hutuswatermelon/NT131.P22/back_end/uploads/1746864863473-entry-1746864863469.jpg

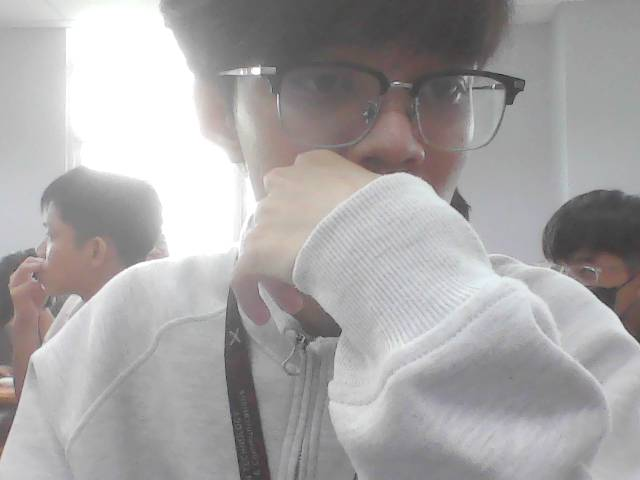
back_end/uploads/1746864863473-entry-1746864863469.jpg
