hutuswatermelon/NT131.P22/back_end/uploads/1746864864985-entry-1746864864979.jpg

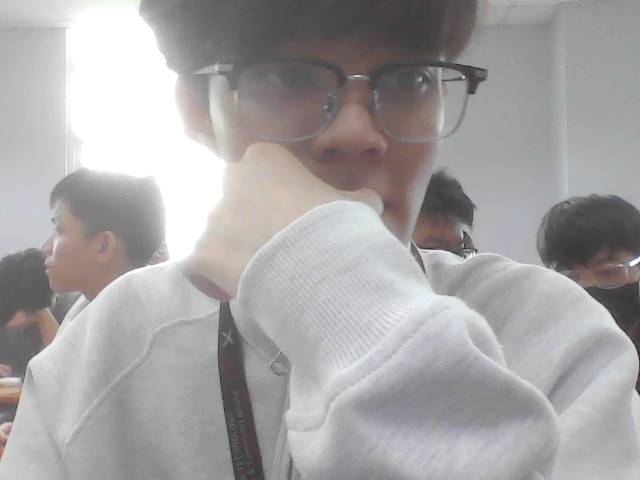
back_end/uploads/1746864864985-entry-1746864864979.jpg
