hutuswatermelon/NT131.P22/back_end/uploads/1746864866506-entry-1746864866501.jpg

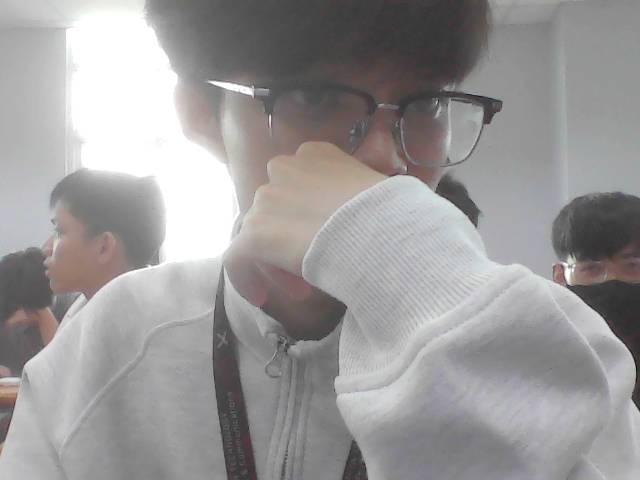
back_end/uploads/1746864866506-entry-1746864866501.jpg
