hutuswatermelon/NT131.P22/back_end/uploads/1746864868323-entry-1746864868013.jpg

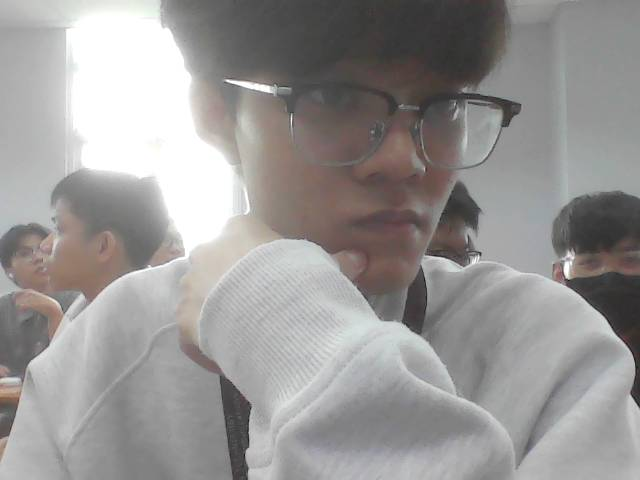
back_end/uploads/1746864868323-entry-1746864868013.jpg
