hutuswatermelon/NT131.P22/back_end/uploads/1746864869845-entry-1746864869527.jpg

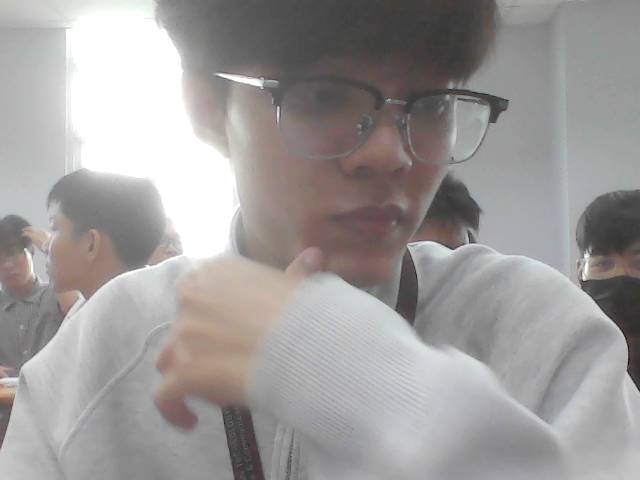
back_end/uploads/1746864869845-entry-1746864869527.jpg
