hutuswatermelon/NT131.P22/back_end/uploads/1746864871052-entry-1746864871045.jpg

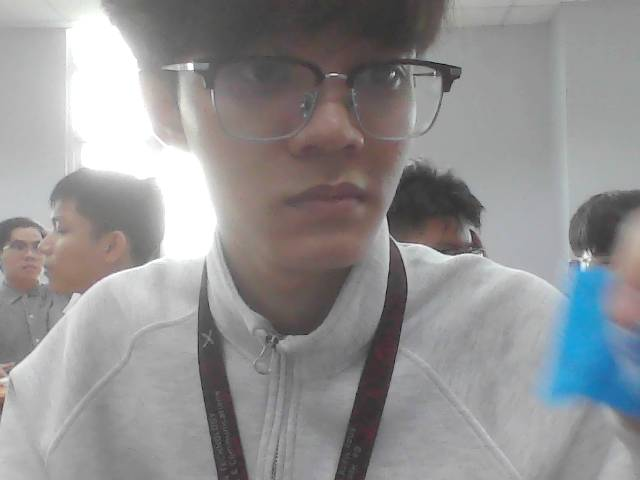
back_end/uploads/1746864871052-entry-1746864871045.jpg
