hutuswatermelon/NT131.P22/back_end/uploads/1746864872554-entry-1746864872549.jpg

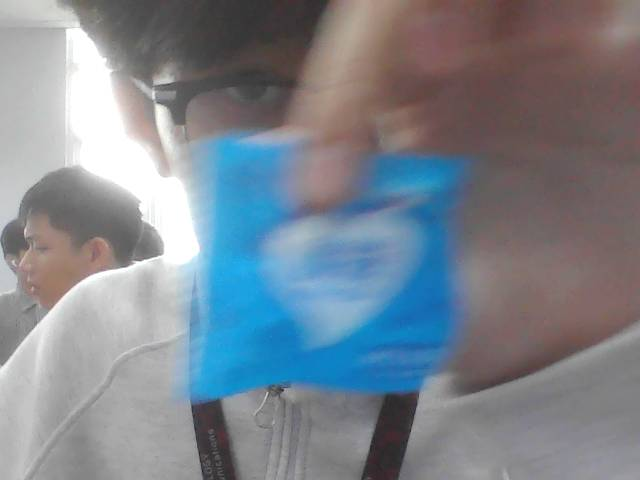
back_end/uploads/1746864872554-entry-1746864872549.jpg
