hutuswatermelon/NT131.P22/back_end/uploads/1746864874057-entry-1746864874053.jpg

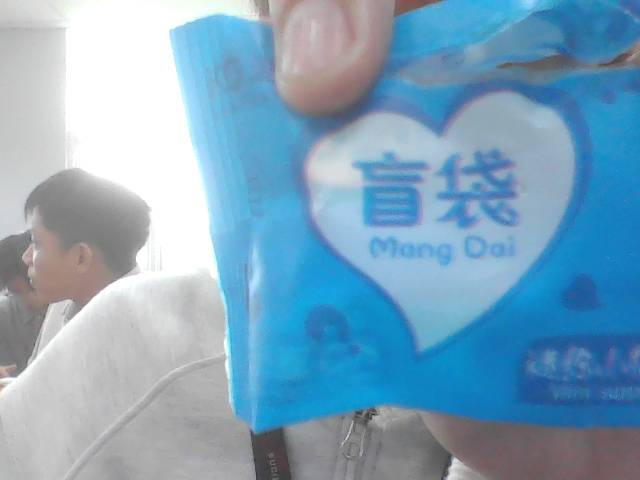
back_end/uploads/1746864874057-entry-1746864874053.jpg
