hutuswatermelon/NT131.P22/back_end/uploads/1746864875561-entry-1746864875557.jpg

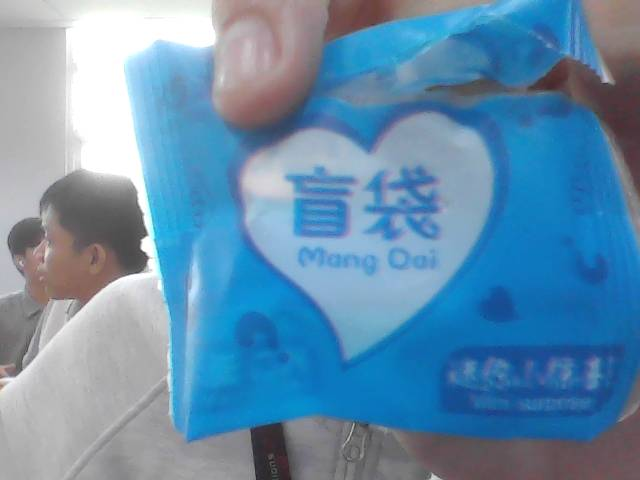
back_end/uploads/1746864875561-entry-1746864875557.jpg
