hutuswatermelon/NT131.P22/back_end/uploads/1746864877072-entry-1746864877068.jpg

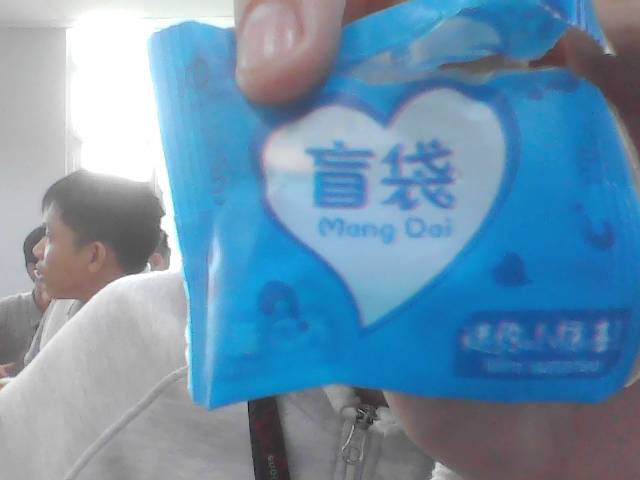
back_end/uploads/1746864877072-entry-1746864877068.jpg
