hutuswatermelon/NT131.P22/back_end/uploads/1746867527541-entry-1746867527536.jpg

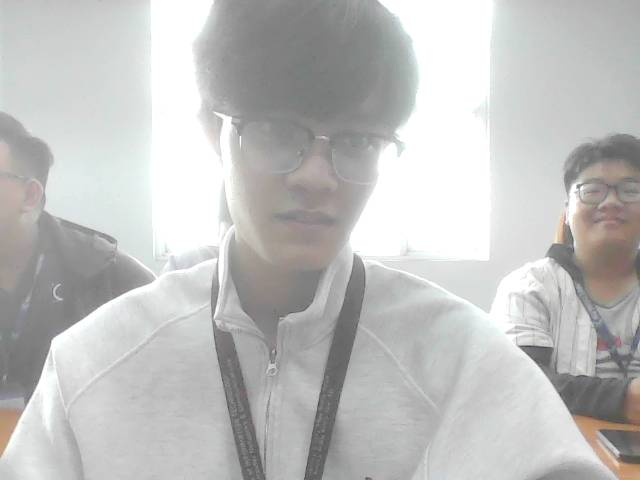
back_end/uploads/1746867527541-entry-1746867527536.jpg
