hutuswatermelon/NT131.P22/back_end/uploads/1746868455816-entry-1746868455803.jpg

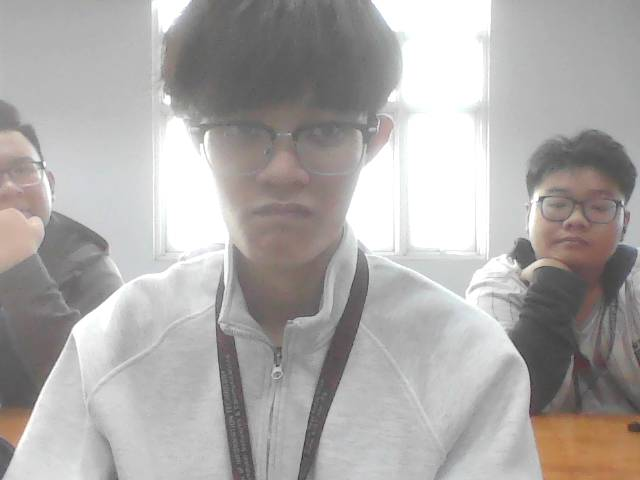
back_end/uploads/1746868455816-entry-1746868455803.jpg
