hutuswatermelon/NT131.P22/back_end/uploads/1746953575087-entry-1746953575075.jpg

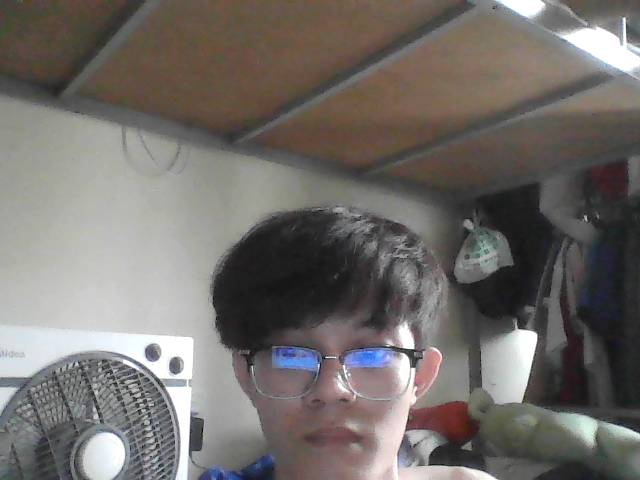
back_end/uploads/1746953575087-entry-1746953575075.jpg
