hutuswatermelon/NT131.P22/back_end/uploads/1746959261396-entry-1746959261392.jpg

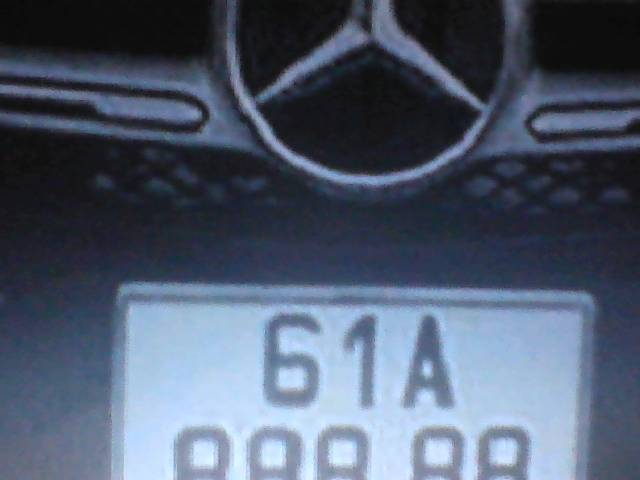
back_end/uploads/1746959261396-entry-1746959261392.jpg
