hutuswatermelon/NT131.P22/back_end/uploads/1746959275397-entry-1746959275392.jpg

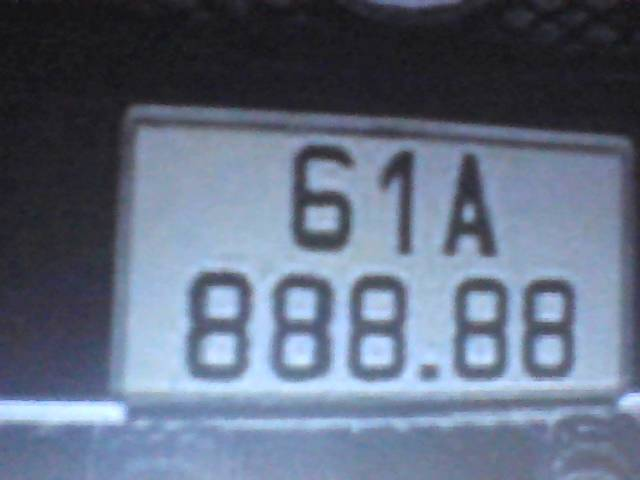
back_end/uploads/1746959275397-entry-1746959275392.jpg
