hutuswatermelon/NT131.P22/back_end/uploads/1746959362127-entry-1746959362123.jpg

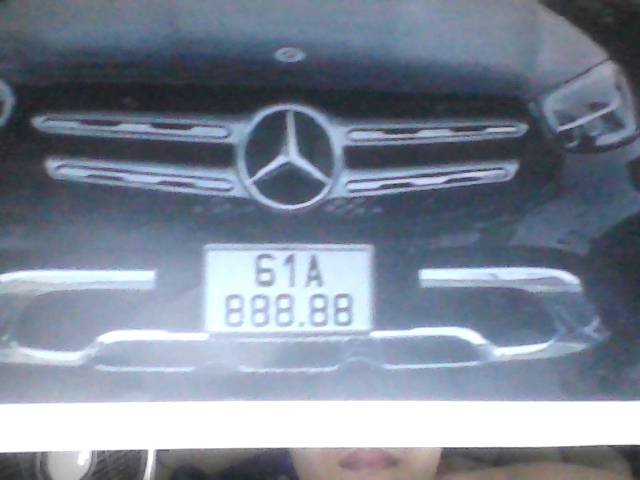
back_end/uploads/1746959362127-entry-1746959362123.jpg
