hutuswatermelon/NT131.P22/back_end/uploads/1746978081845-entry-1746978081831.jpg

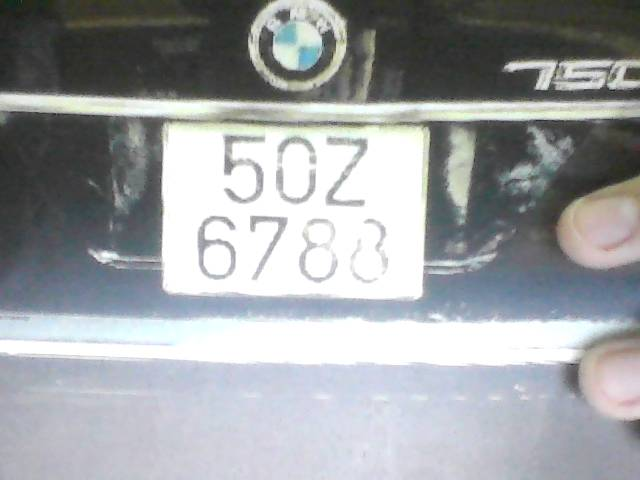
back_end/uploads/1746978081845-entry-1746978081831.jpg
