hutuswatermelon/NT131.P22/back_end/uploads/1746978145780-entry-1746978145776.jpg

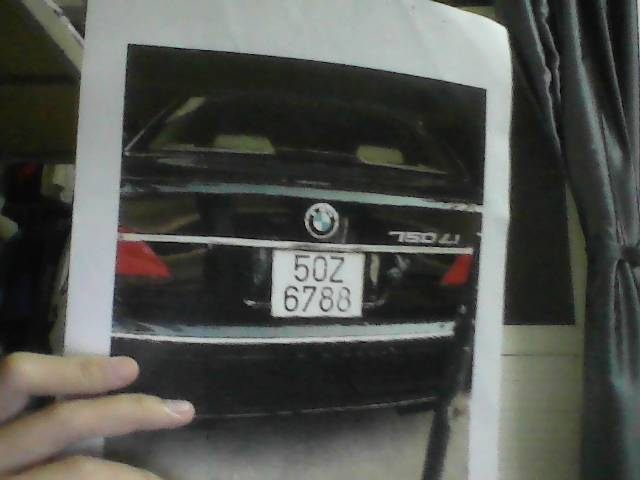
back_end/uploads/1746978145780-entry-1746978145776.jpg
