hutuswatermelon/NT131.P22/back_end/uploads/1746978197605-entry-1746978197599.jpg

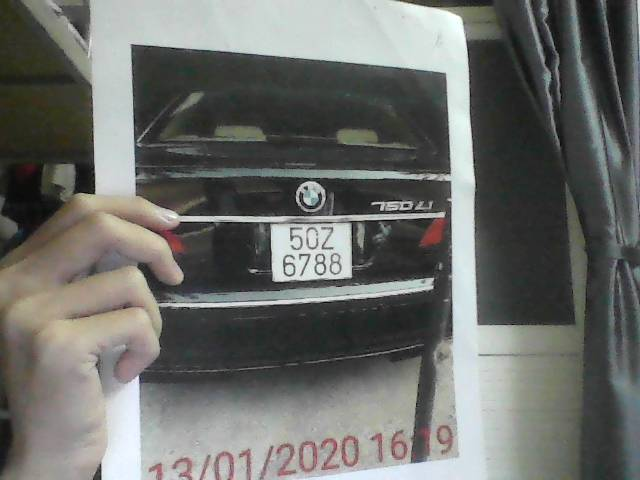
back_end/uploads/1746978197605-entry-1746978197599.jpg
