hutuswatermelon/NT131.P22/back_end/uploads/1746978227795-entry-1746978227792.jpg

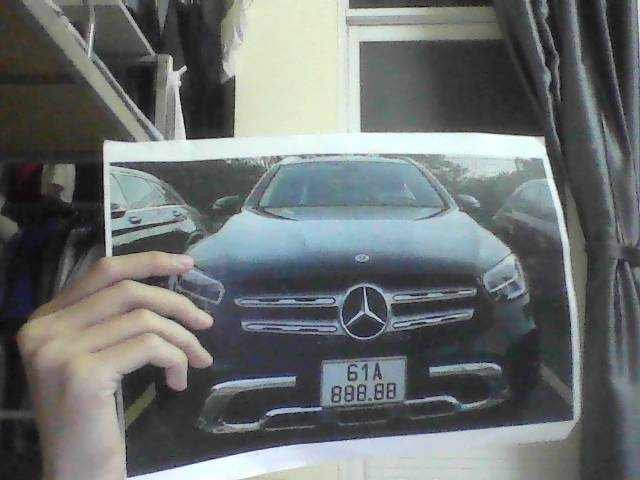
back_end/uploads/1746978227795-entry-1746978227792.jpg
