hutuswatermelon/NT131.P22/back_end/uploads/1746978264536-entry-1746978264530.jpg

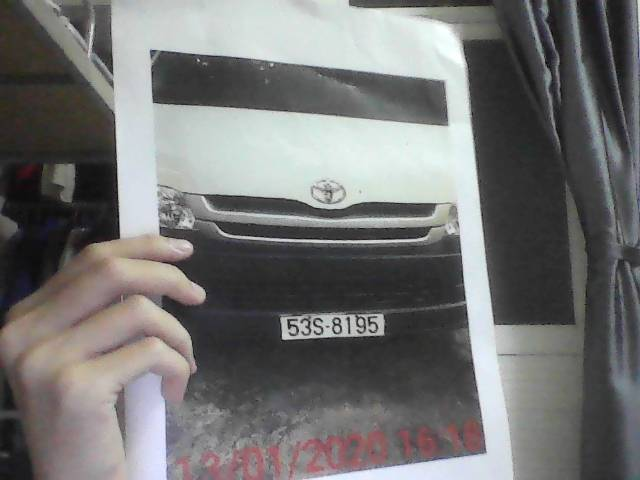
back_end/uploads/1746978264536-entry-1746978264530.jpg
