hutuswatermelon/NT131.P22/back_end/uploads/1746978326046-entry-1746978326043.jpg

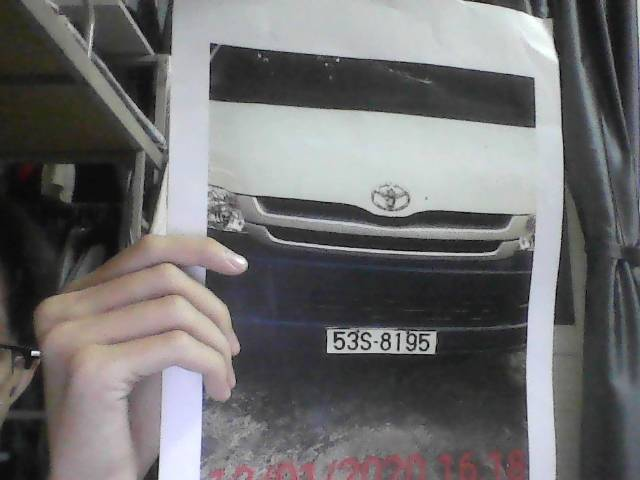
back_end/uploads/1746978326046-entry-1746978326043.jpg
