hutuswatermelon/NT131.P22/back_end/uploads/1746978920150-entry-1746978920143.jpg

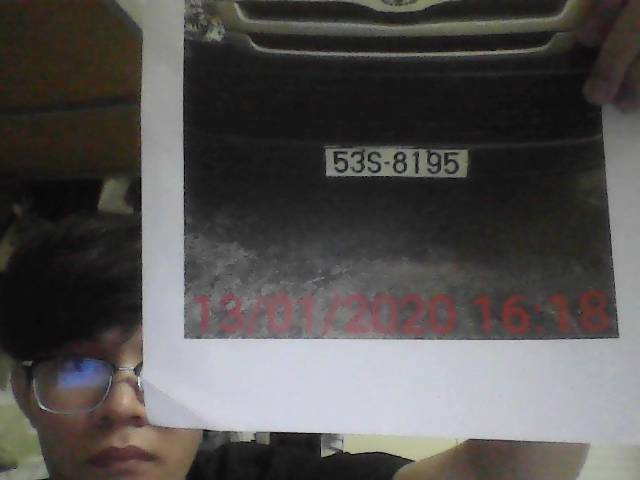
back_end/uploads/1746978920150-entry-1746978920143.jpg
