hutuswatermelon/NT131.P22/back_end/uploads/1746978947929-entry-1746978947927.jpg

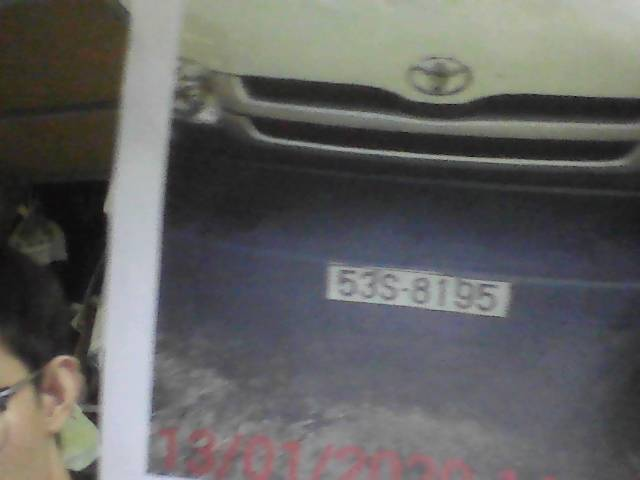
back_end/uploads/1746978947929-entry-1746978947927.jpg
