hutuswatermelon/NT131.P22/back_end/uploads/1746978972538-entry-1746978972531.jpg

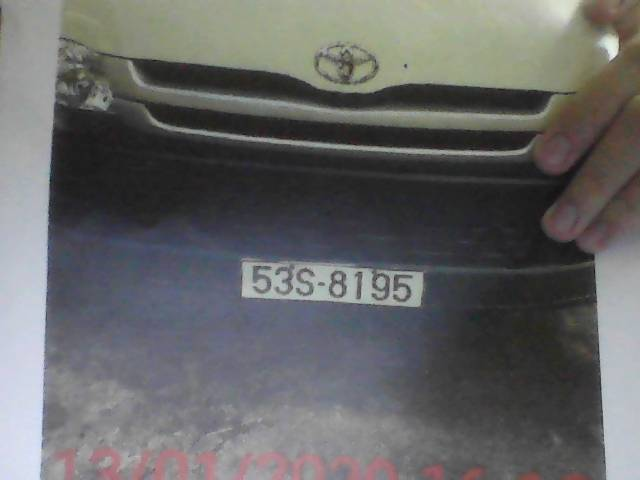
back_end/uploads/1746978972538-entry-1746978972531.jpg
