hutuswatermelon/NT131.P22/back_end/uploads/1746979031061-entry-1746979031053.jpg

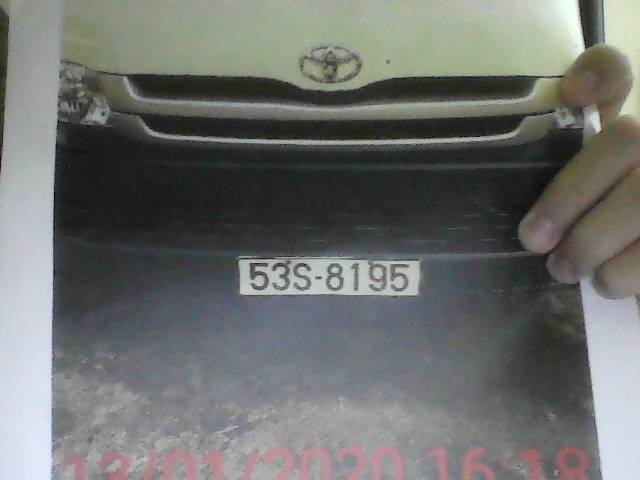
back_end/uploads/1746979031061-entry-1746979031053.jpg
