hutuswatermelon/NT131.P22/back_end/uploads/1746981746926-entry-1746981746917.jpg

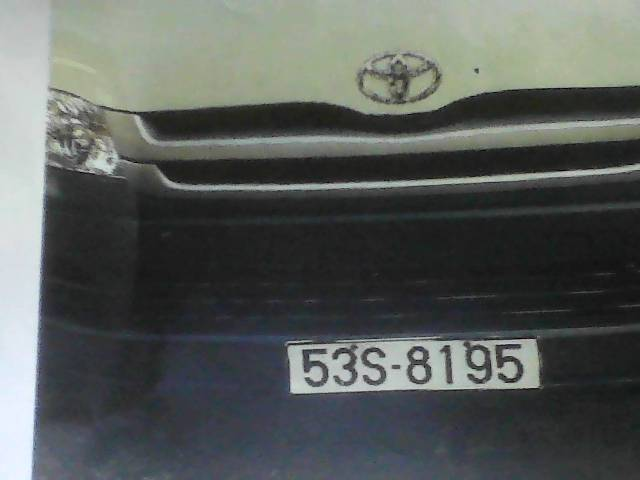
back_end/uploads/1746981746926-entry-1746981746917.jpg
