hutuswatermelon/NT131.P22/back_end/uploads/1746981779292-entry-1746981779285.jpg

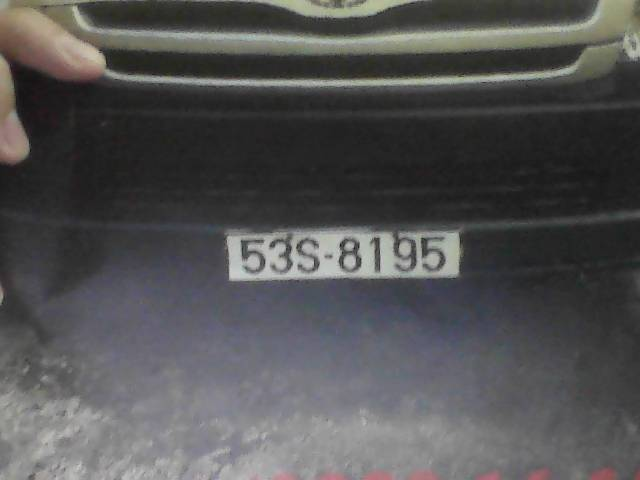
back_end/uploads/1746981779292-entry-1746981779285.jpg
