hutuswatermelon/NT131.P22/back_end/uploads/1746981790187-entry-1746981790183.jpg

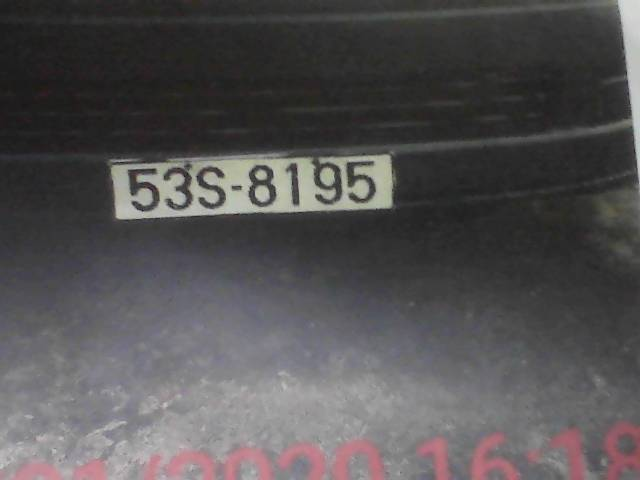
back_end/uploads/1746981790187-entry-1746981790183.jpg
