hutuswatermelon/NT131.P22/back_end/uploads/1746981802821-entry-1746981802512.jpg

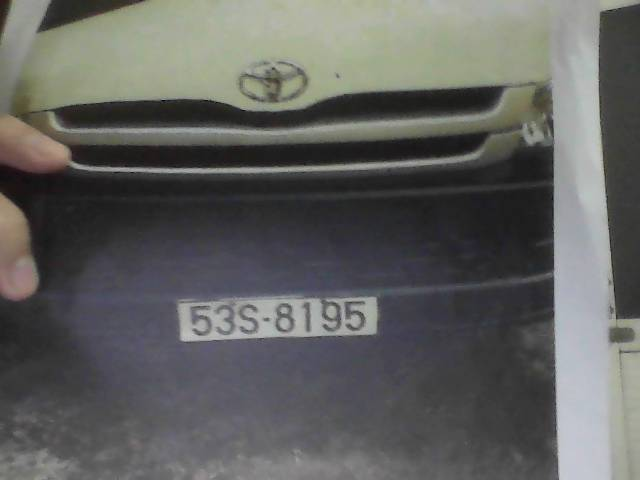
back_end/uploads/1746981802821-entry-1746981802512.jpg
