hutuswatermelon/NT131.P22/back_end/uploads/1746981819778-entry-1746981819770.jpg

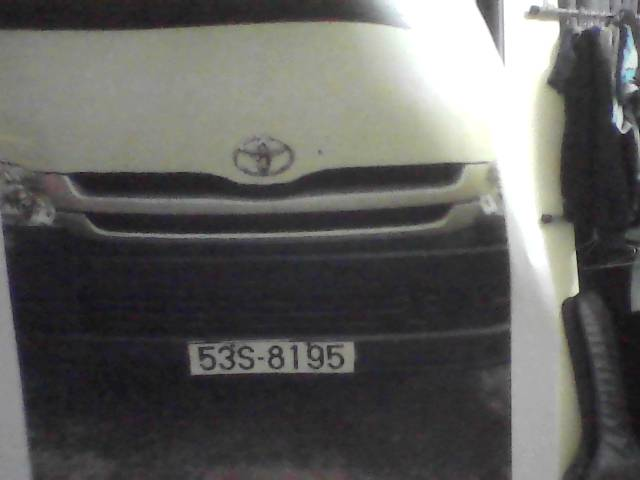
back_end/uploads/1746981819778-entry-1746981819770.jpg
