hutuswatermelon/NT131.P22/back_end/uploads/1746982269582-entry-1746982269579.jpg

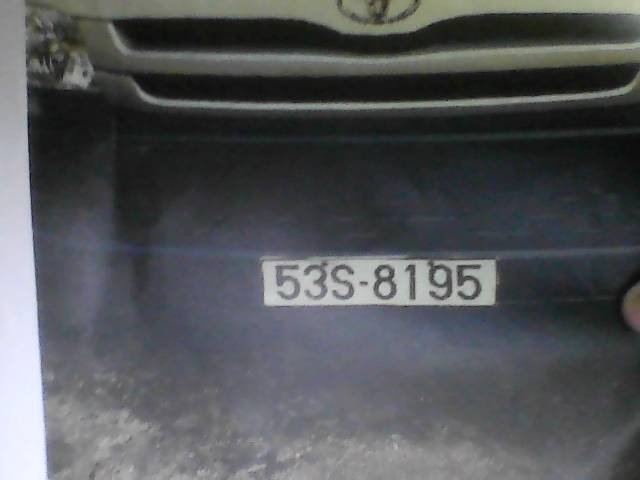
back_end/uploads/1746982269582-entry-1746982269579.jpg
