hutuswatermelon/NT131.P22/back_end/uploads/1746982297239-entry-1746982297234.jpg

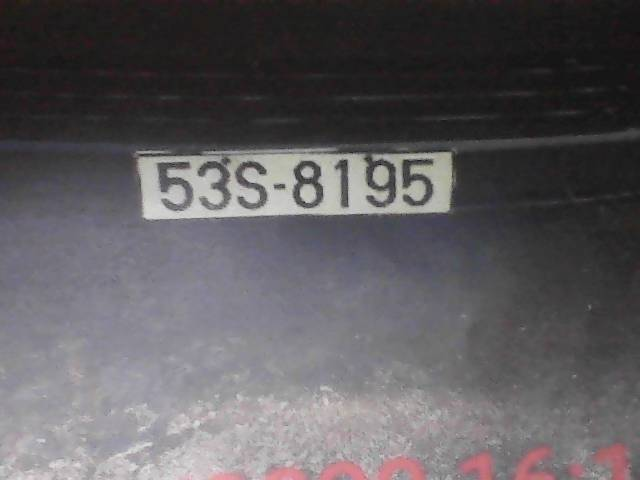
back_end/uploads/1746982297239-entry-1746982297234.jpg
