hutuswatermelon/NT131.P22/back_end/uploads/1746982308922-entry-1746982308920.jpg

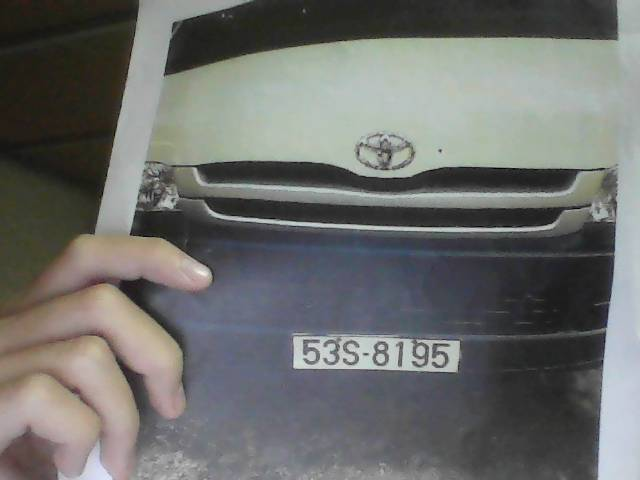
back_end/uploads/1746982308922-entry-1746982308920.jpg
