hutuswatermelon/NT131.P22/back_end/uploads/1746982318628-entry-1746982318623.jpg

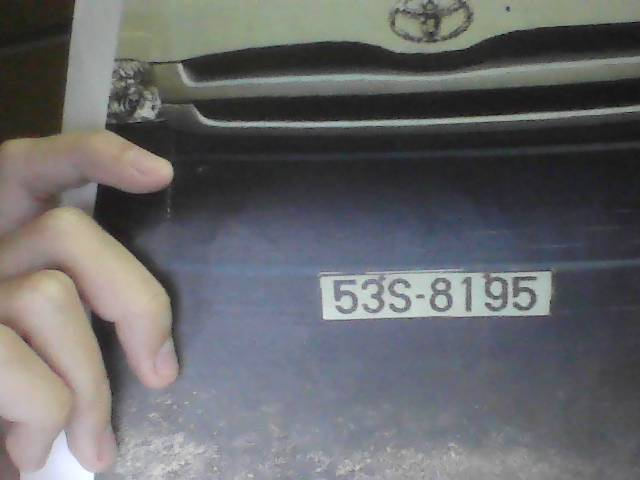
back_end/uploads/1746982318628-entry-1746982318623.jpg
