hutuswatermelon/NT131.P22/back_end/uploads/1746982329878-entry-1746982329874.jpg

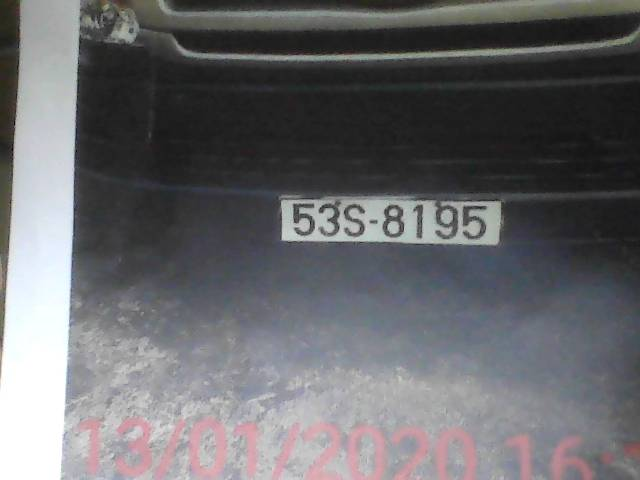
back_end/uploads/1746982329878-entry-1746982329874.jpg
