hutuswatermelon/NT131.P22/back_end/uploads/1746982339927-entry-1746982339925.jpg

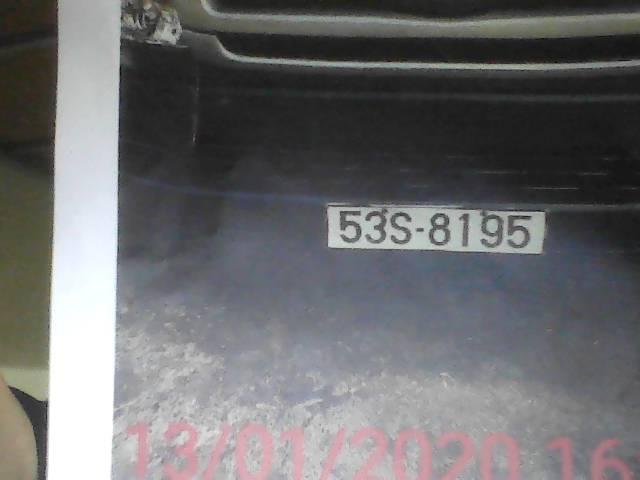
back_end/uploads/1746982339927-entry-1746982339925.jpg
