hutuswatermelon/NT131.P22/back_end/uploads/1746982353290-entry-1746982353286.jpg

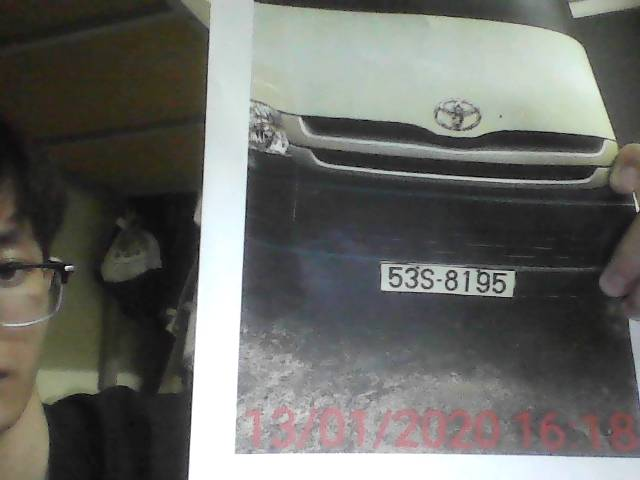
back_end/uploads/1746982353290-entry-1746982353286.jpg
