hutuswatermelon/NT131.P22/back_end/uploads/1746990870169-entry-1746990870156.jpg

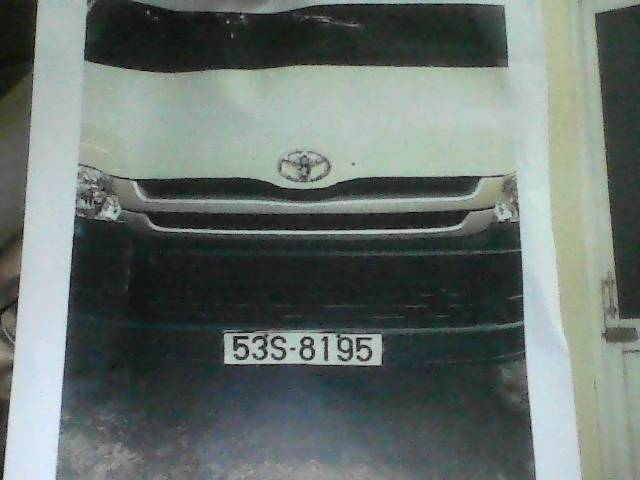
back_end/uploads/1746990870169-entry-1746990870156.jpg
