hutuswatermelon/NT131.P22/back_end/uploads/1746990877798-entry-1746990877794.jpg

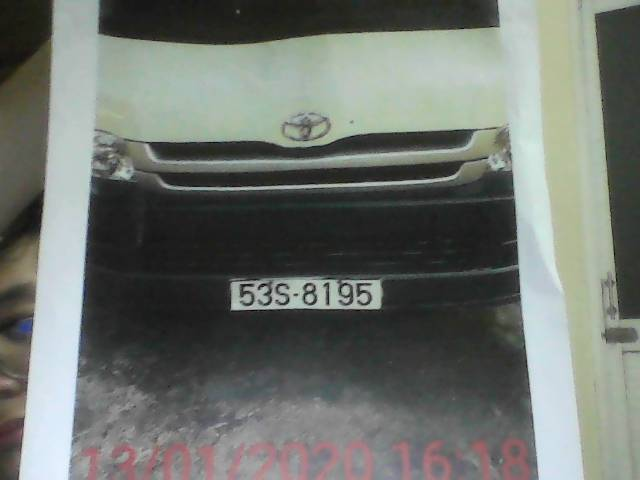
back_end/uploads/1746990877798-entry-1746990877794.jpg
