hutuswatermelon/NT131.P22/back_end/uploads/1746990892995-entry-1746990892991.jpg

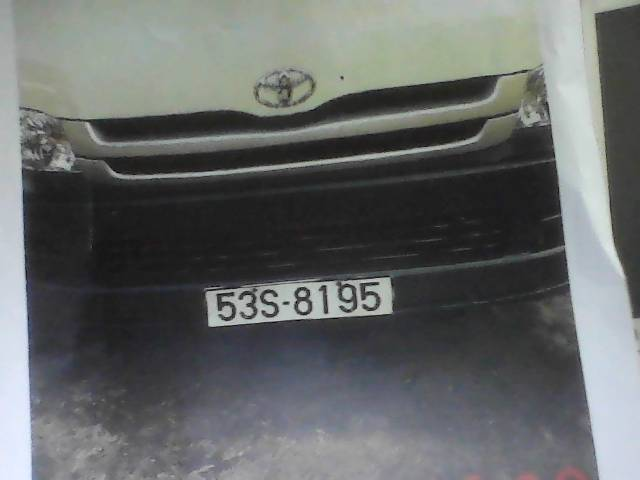
back_end/uploads/1746990892995-entry-1746990892991.jpg
