hutuswatermelon/NT131.P22/back_end/uploads/1746990904815-entry-1746990904812.jpg

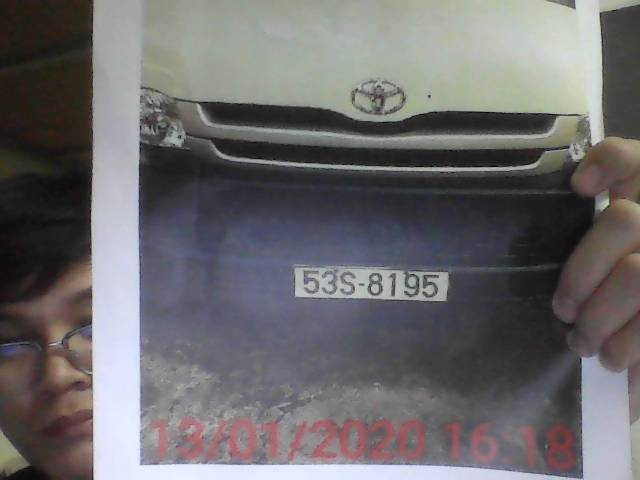
back_end/uploads/1746990904815-entry-1746990904812.jpg
