hutuswatermelon/NT131.P22/back_end/uploads/1746990915697-entry-1746990915695.jpg

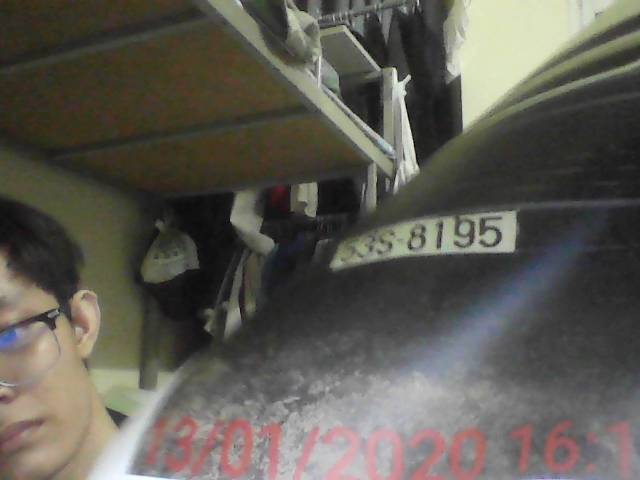
back_end/uploads/1746990915697-entry-1746990915695.jpg
