hutuswatermelon/NT131.P22/back_end/uploads/1746990925098-entry-1746990925093.jpg

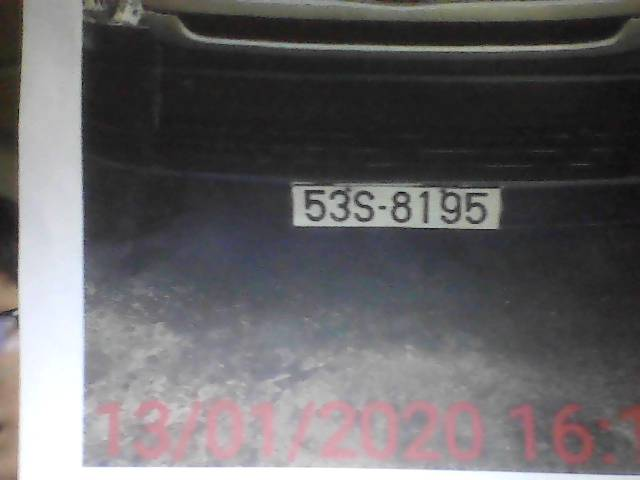
back_end/uploads/1746990925098-entry-1746990925093.jpg
