hutuswatermelon/NT131.P22/back_end/uploads/1746990991744-entry-1746990991741.jpg

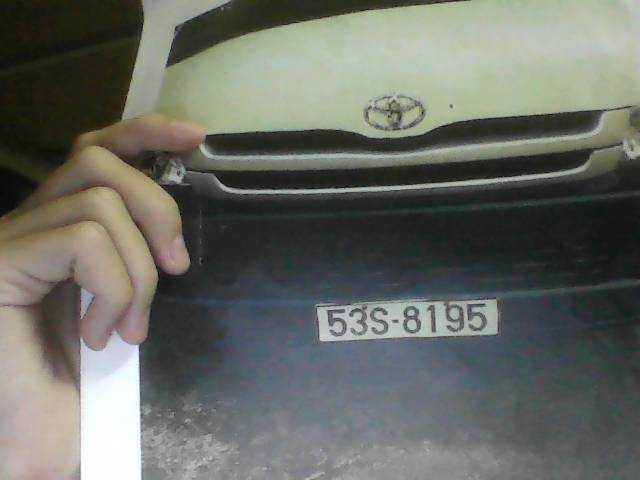
back_end/uploads/1746990991744-entry-1746990991741.jpg
