hutuswatermelon/NT131.P22/back_end/uploads/1746991083994-entry-1746991083988.jpg

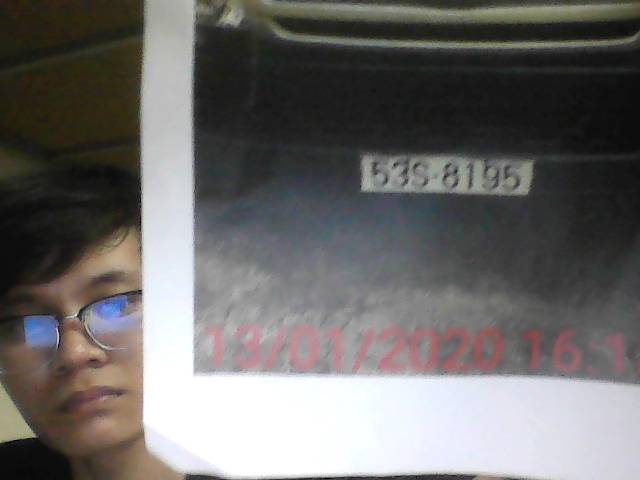
back_end/uploads/1746991083994-entry-1746991083988.jpg
