hutuswatermelon/NT131.P22/back_end/uploads/1746991093643-entry-1746991093639.jpg

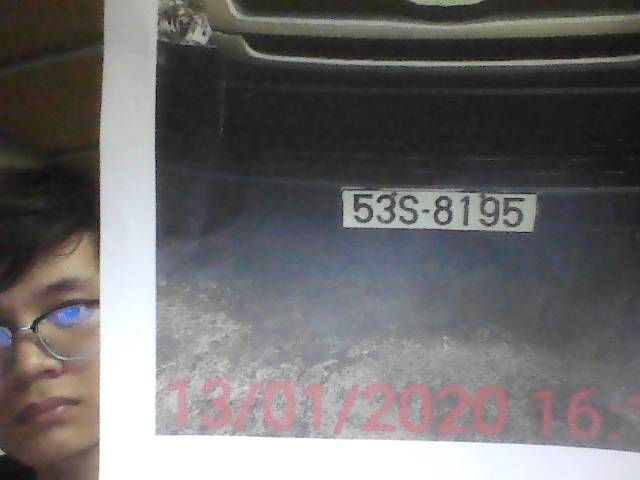
back_end/uploads/1746991093643-entry-1746991093639.jpg
