hutuswatermelon/NT131.P22/back_end/uploads/1746991432287-entry-1746991432284.jpg

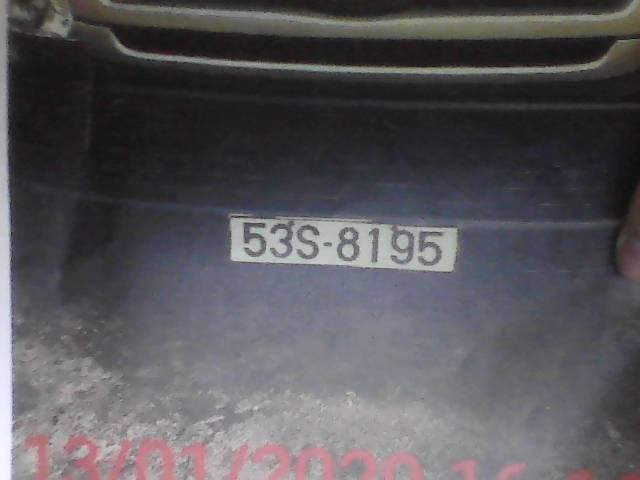
back_end/uploads/1746991432287-entry-1746991432284.jpg
