hutuswatermelon/NT131.P22/back_end/uploads/1746991441638-entry-1746991441635.jpg

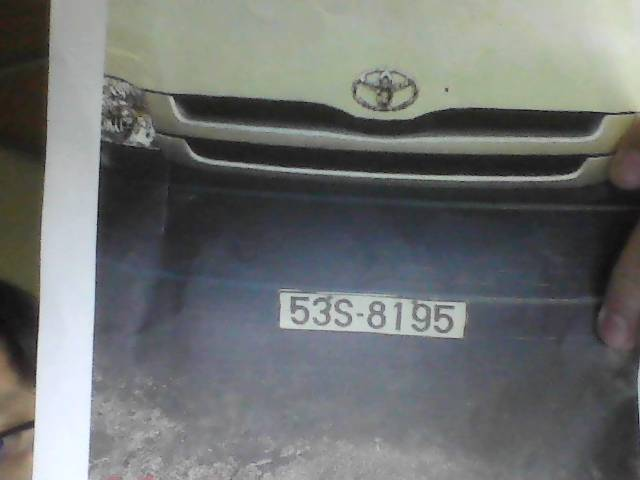
back_end/uploads/1746991441638-entry-1746991441635.jpg
