hutuswatermelon/NT131.P22/back_end/uploads/1746991452036-entry-1746991452033.jpg

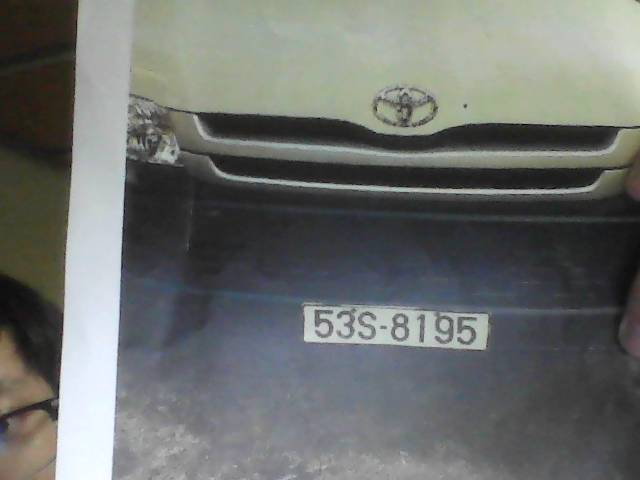
back_end/uploads/1746991452036-entry-1746991452033.jpg
