hutuswatermelon/NT131.P22/back_end/uploads/1746991681770-entry-1746991681767.jpg

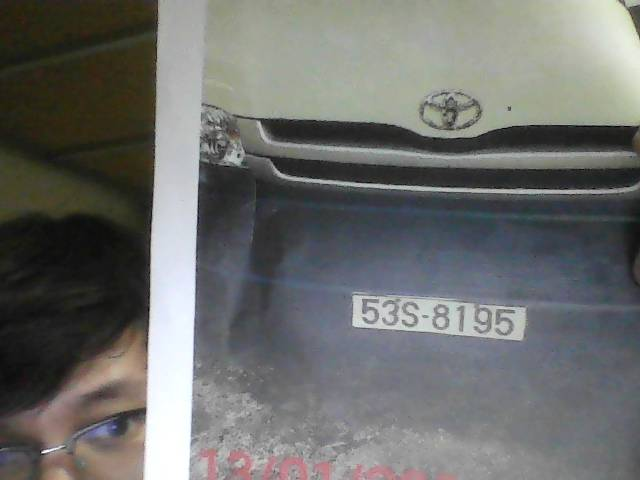
back_end/uploads/1746991681770-entry-1746991681767.jpg
