hutuswatermelon/NT131.P22/back_end/uploads/1746991689409-entry-1746991689407.jpg

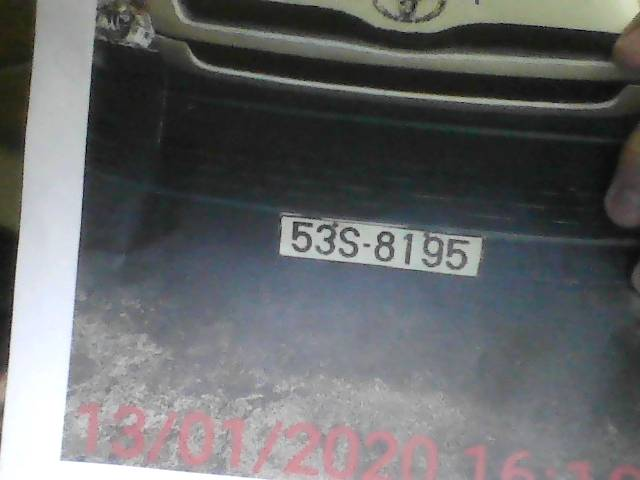
back_end/uploads/1746991689409-entry-1746991689407.jpg
