hutuswatermelon/NT131.P22/back_end/uploads/1746991702769-entry-1746991702767.jpg

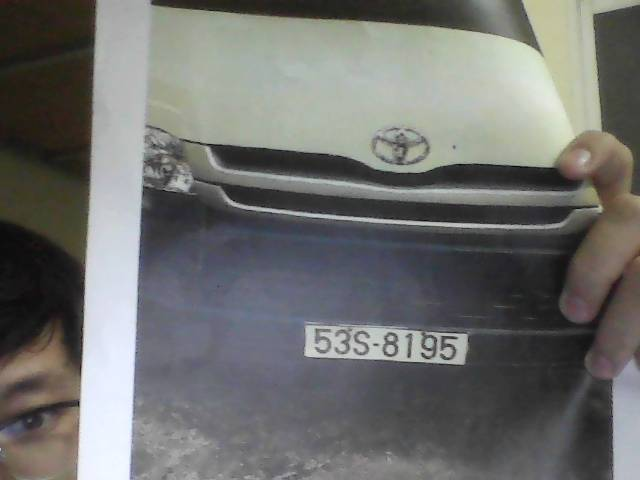
back_end/uploads/1746991702769-entry-1746991702767.jpg
