hutuswatermelon/NT131.P22/back_end/uploads/1746991738052-entry-1746991738047.jpg

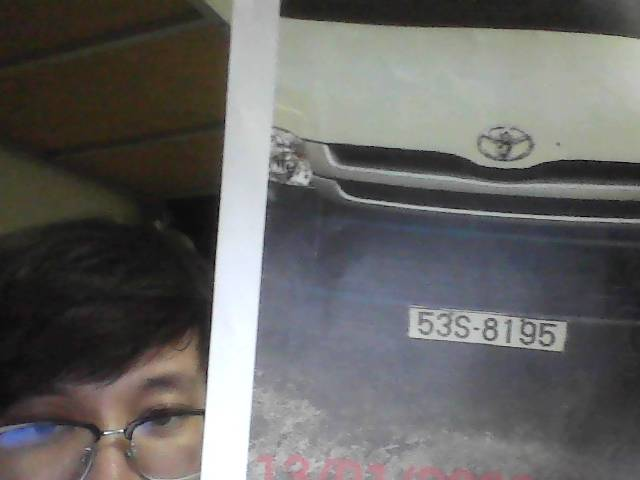
back_end/uploads/1746991738052-entry-1746991738047.jpg
