hutuswatermelon/NT131.P22/back_end/uploads/1746991766396-entry-1746991766393.jpg

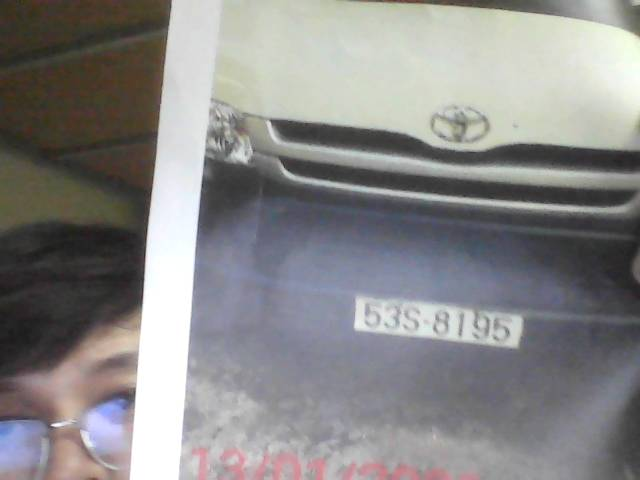
back_end/uploads/1746991766396-entry-1746991766393.jpg
