hutuswatermelon/NT131.P22/back_end/uploads/1746991775759-entry-1746991775756.jpg

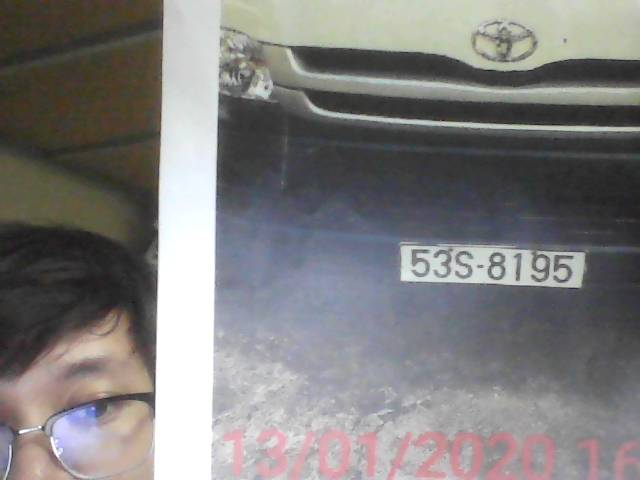
back_end/uploads/1746991775759-entry-1746991775756.jpg
