hutuswatermelon/NT131.P22/back_end/uploads/1746991833990-entry-1746991833987.jpg

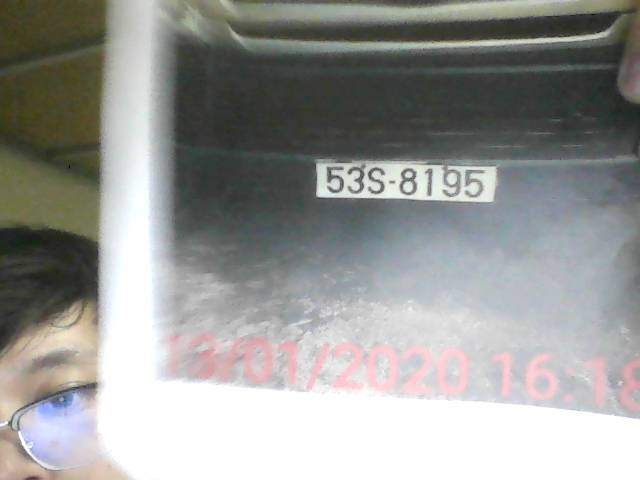
back_end/uploads/1746991833990-entry-1746991833987.jpg
