hutuswatermelon/NT131.P22/back_end/uploads/1746991848024-entry-1746991848020.jpg

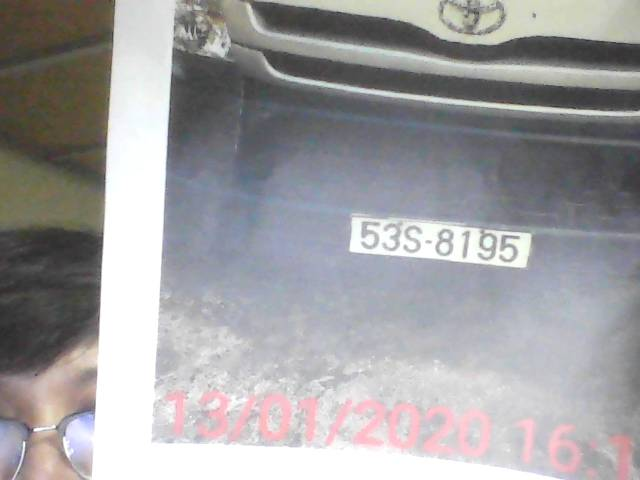
back_end/uploads/1746991848024-entry-1746991848020.jpg
