hutuswatermelon/NT131.P22/back_end/uploads/1746991893759-entry-1746991893755.jpg

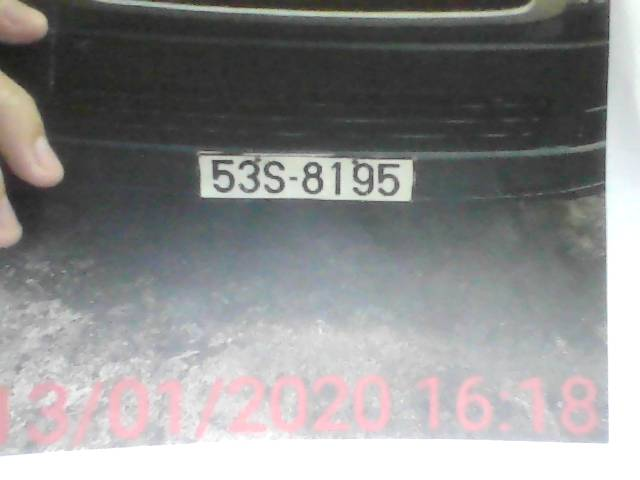
back_end/uploads/1746991893759-entry-1746991893755.jpg
