hutuswatermelon/NT131.P22/back_end/uploads/1746992456463-entry-1746992456459.jpg

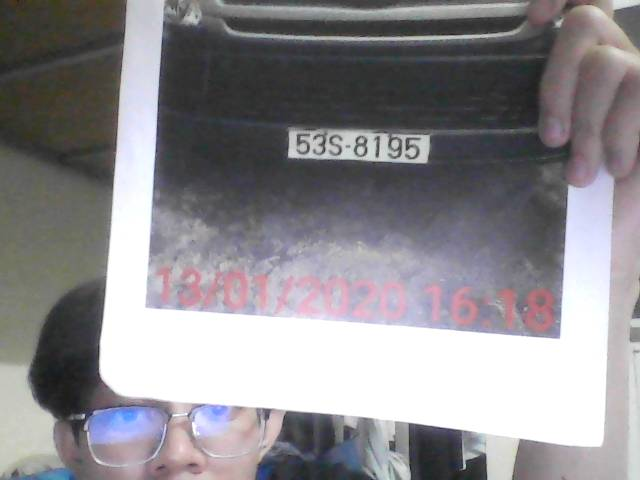
back_end/uploads/1746992456463-entry-1746992456459.jpg
