hutuswatermelon/NT131.P22/back_end/uploads/1747031487131-entry-1747031487115.jpg

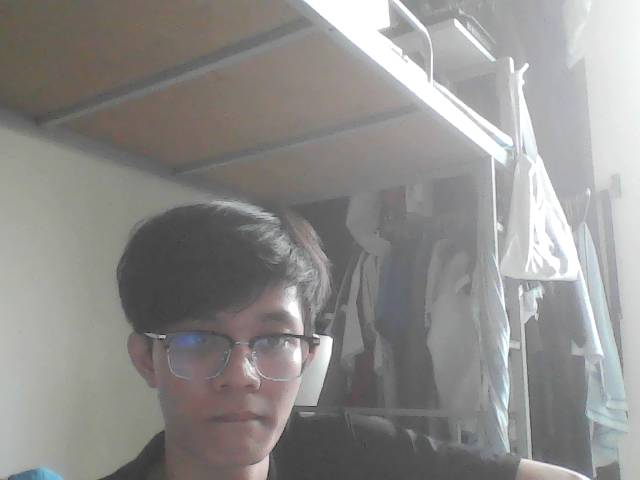
back_end/uploads/1747031487131-entry-1747031487115.jpg
