hutuswatermelon/NT131.P22/back_end/uploads/1747031562585-entry-1747031562582.jpg

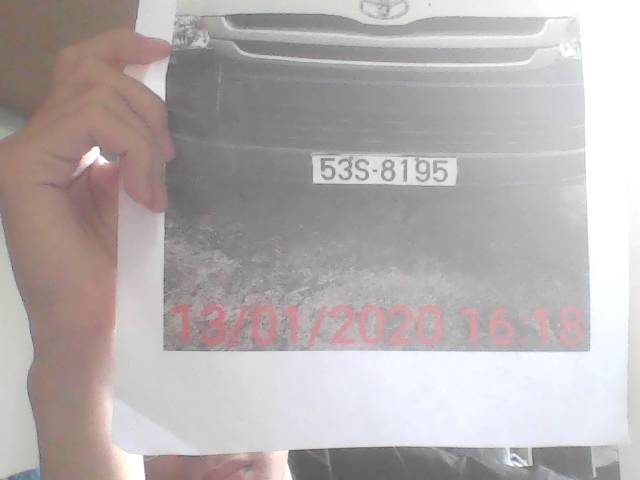
back_end/uploads/1747031562585-entry-1747031562582.jpg
