hutuswatermelon/NT131.P22/back_end/uploads/1747031672830-exit-1747031672827.jpg

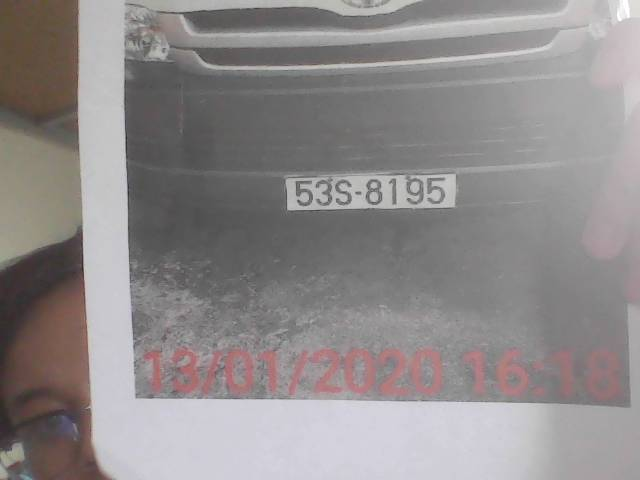
back_end/uploads/1747031672830-exit-1747031672827.jpg
