hutuswatermelon/NT131.P22/back_end/uploads/1747031699318-exit-1747031699316.jpg

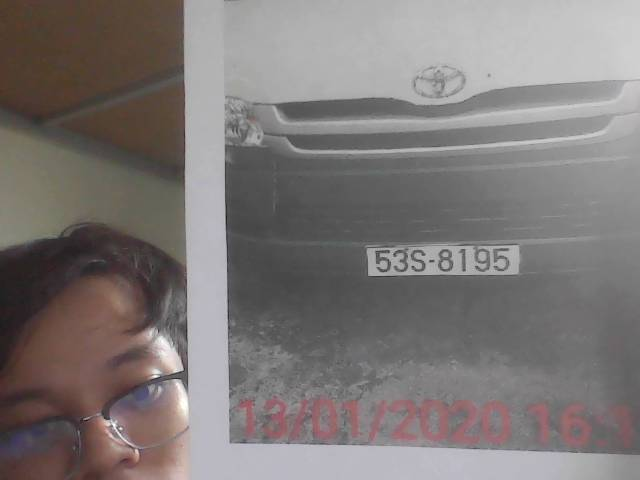
back_end/uploads/1747031699318-exit-1747031699316.jpg
