hutuswatermelon/NT131.P22/back_end/uploads/1747042673337-entry-1747042673323.jpg

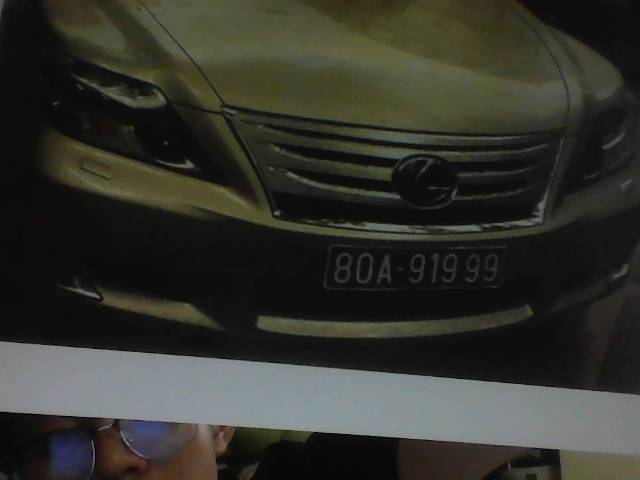
back_end/uploads/1747042673337-entry-1747042673323.jpg
