hutuswatermelon/NT131.P22/back_end/uploads/1747042683621-entry-1747042683617.jpg

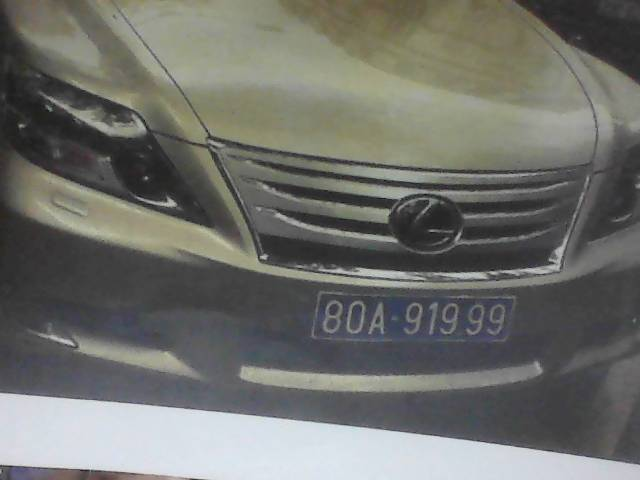
back_end/uploads/1747042683621-entry-1747042683617.jpg
