hutuswatermelon/NT131.P22/back_end/uploads/1747042701676-entry-1747042701672.jpg

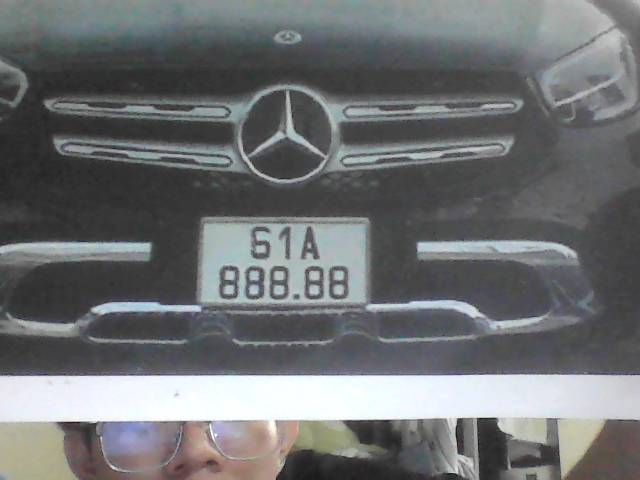
back_end/uploads/1747042701676-entry-1747042701672.jpg
