hutuswatermelon/NT131.P22/back_end/uploads/1747042712956-entry-1747042712948.jpg

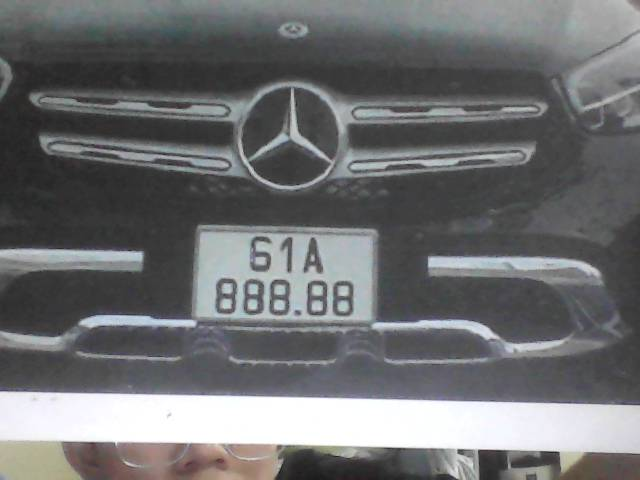
back_end/uploads/1747042712956-entry-1747042712948.jpg
