hutuswatermelon/NT131.P22/back_end/uploads/1747042752693-entry-1747042752687.jpg

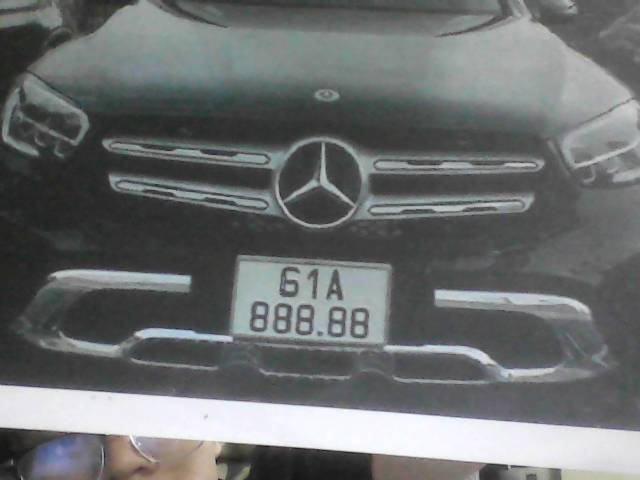
back_end/uploads/1747042752693-entry-1747042752687.jpg
