hutuswatermelon/NT131.P22/back_end/uploads/1747042763056-entry-1747042763051.jpg

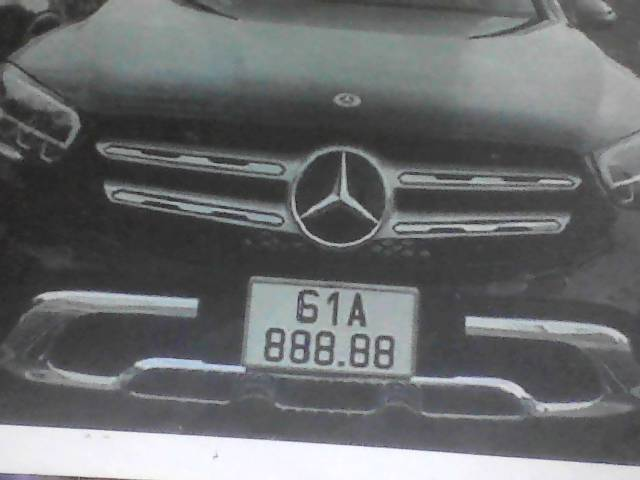
back_end/uploads/1747042763056-entry-1747042763051.jpg
