hutuswatermelon/NT131.P22/back_end/uploads/1747042785964-entry-1747042785958.jpg

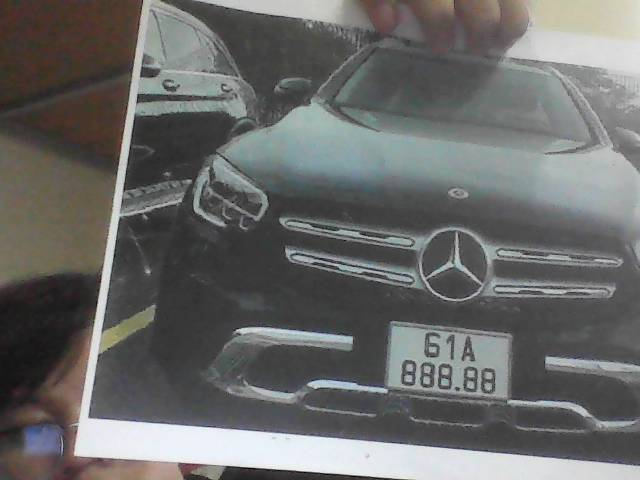
back_end/uploads/1747042785964-entry-1747042785958.jpg
