hutuswatermelon/NT131.P22/back_end/uploads/1747042799372-entry-1747042799365.jpg

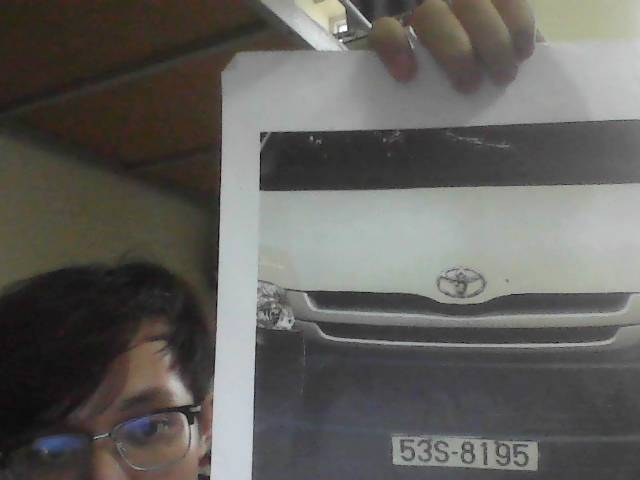
back_end/uploads/1747042799372-entry-1747042799365.jpg
