hutuswatermelon/NT131.P22/back_end/uploads/1747042811032-entry-1747042811027.jpg

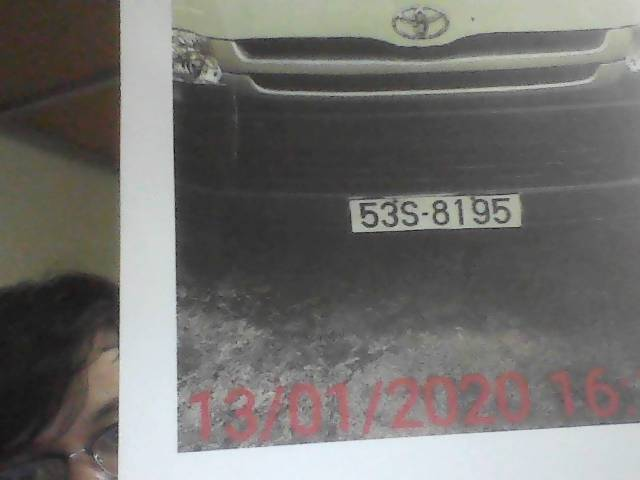
back_end/uploads/1747042811032-entry-1747042811027.jpg
