hutuswatermelon/NT131.P22/back_end/uploads/1747042822264-entry-1747042822259.jpg

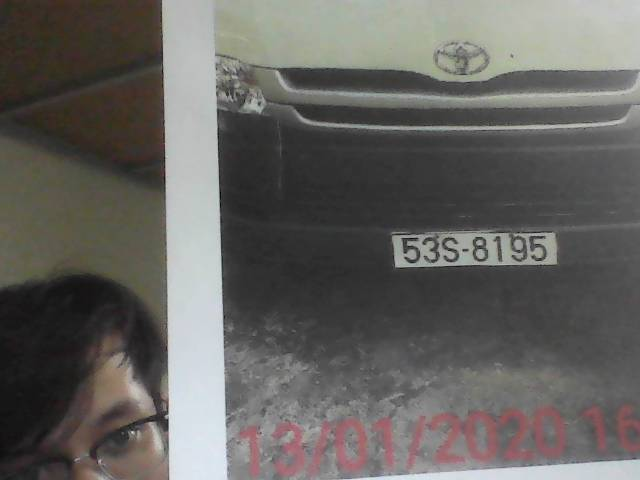
back_end/uploads/1747042822264-entry-1747042822259.jpg
