hutuswatermelon/NT131.P22/back_end/uploads/1747042833515-entry-1747042833511.jpg

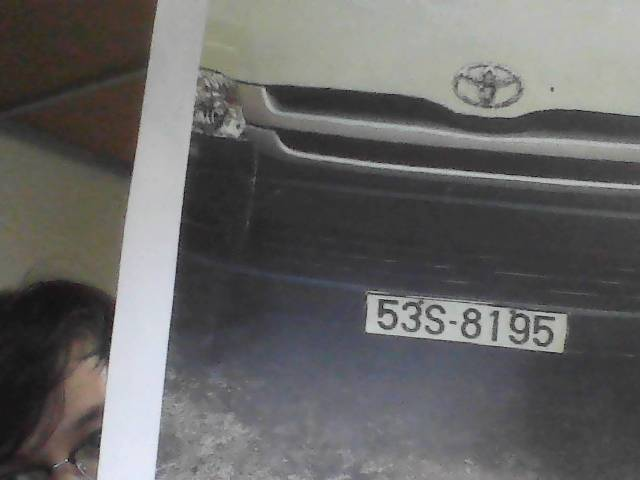
back_end/uploads/1747042833515-entry-1747042833511.jpg
