hutuswatermelon/NT131.P22/back_end/uploads/1747043046608-entry-1747043046603.jpg

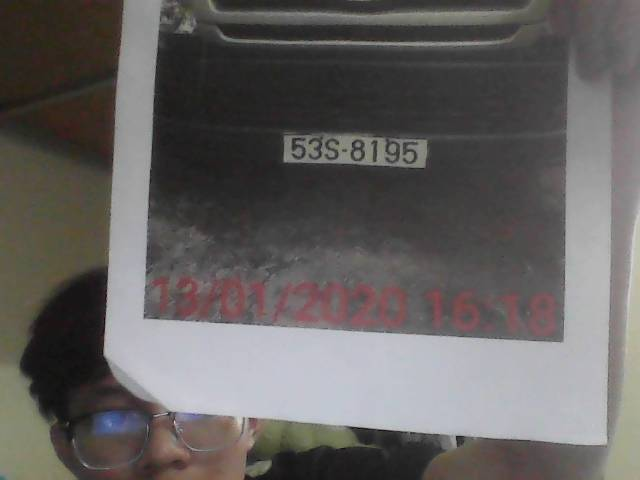
back_end/uploads/1747043046608-entry-1747043046603.jpg
