hutuswatermelon/NT131.P22/back_end/uploads/1747043776199-entry-1747043776194.jpg

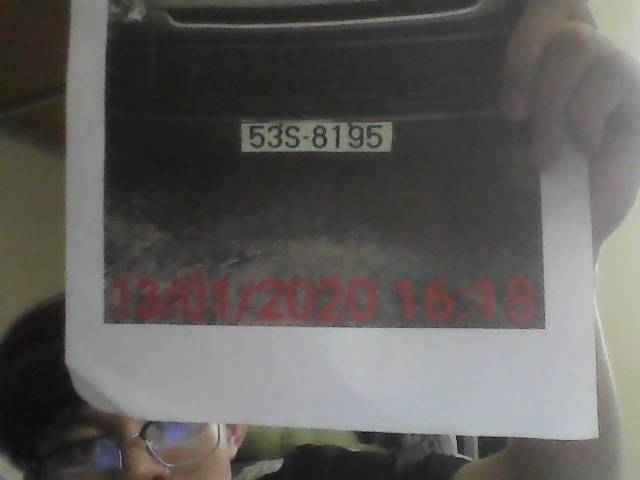
back_end/uploads/1747043776199-entry-1747043776194.jpg
