hutuswatermelon/NT131.P22/back_end/uploads/1747043786472-entry-1747043786467.jpg

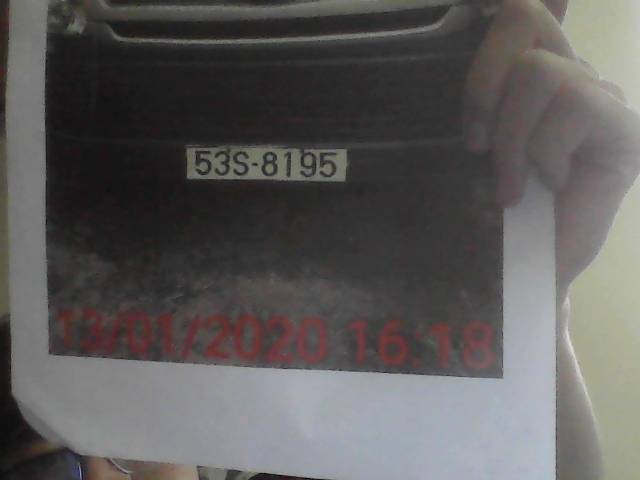
back_end/uploads/1747043786472-entry-1747043786467.jpg
