hutuswatermelon/NT131.P22/back_end/uploads/1747043838865-entry-1747043838862.jpg

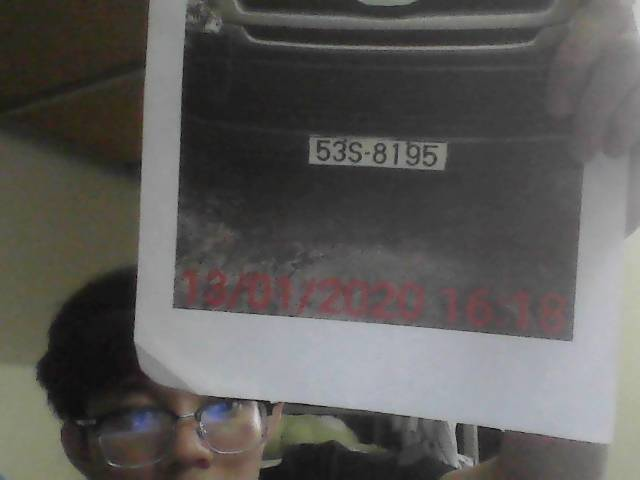
back_end/uploads/1747043838865-entry-1747043838862.jpg
