hutuswatermelon/NT131.P22/back_end/uploads/1747044054107-entry-1747044054103.jpg

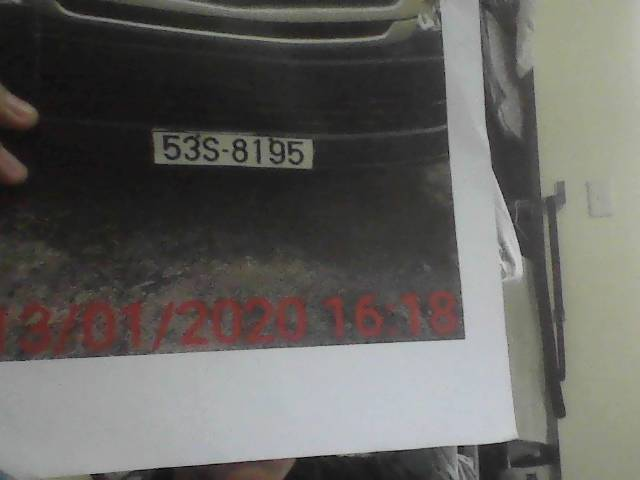
back_end/uploads/1747044054107-entry-1747044054103.jpg
