hutuswatermelon/NT131.P22/back_end/uploads/1747044072528-entry-1747044072524.jpg

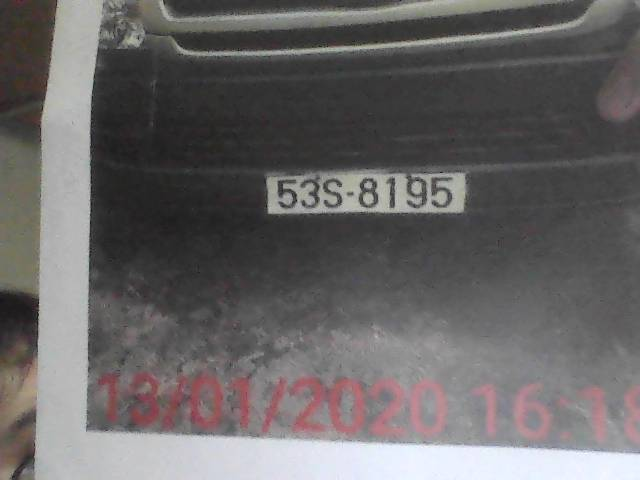
back_end/uploads/1747044072528-entry-1747044072524.jpg
