hutuswatermelon/NT131.P22/back_end/uploads/1747044181487-entry-1747044181477.jpg

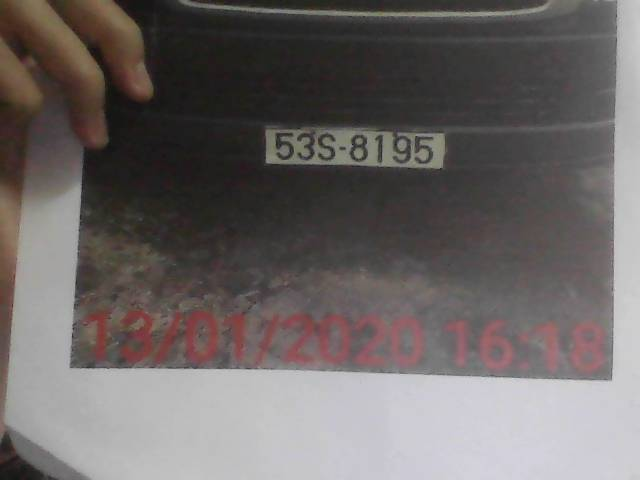
back_end/uploads/1747044181487-entry-1747044181477.jpg
