hutuswatermelon/NT131.P22/back_end/uploads/1747044194484-entry-1747044194480.jpg

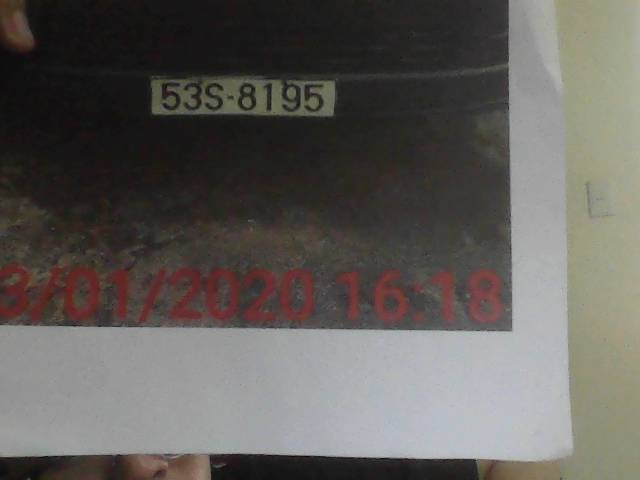
back_end/uploads/1747044194484-entry-1747044194480.jpg
