hutuswatermelon/NT131.P22/back_end/uploads/1747044206288-entry-1747044206283.jpg

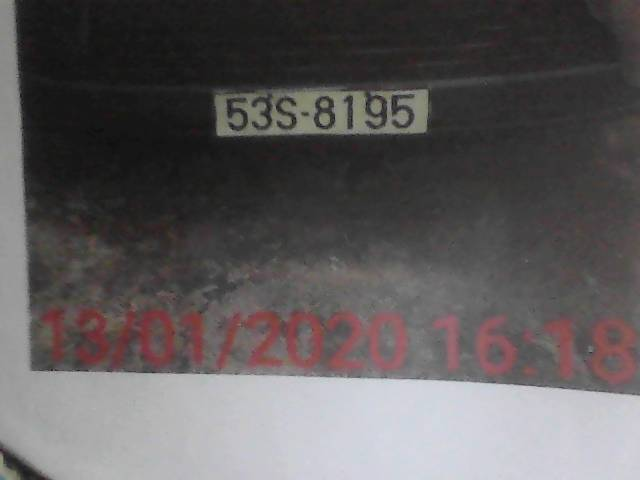
back_end/uploads/1747044206288-entry-1747044206283.jpg
