hutuswatermelon/NT131.P22/back_end/uploads/1747044213636-entry-1747044213633.jpg

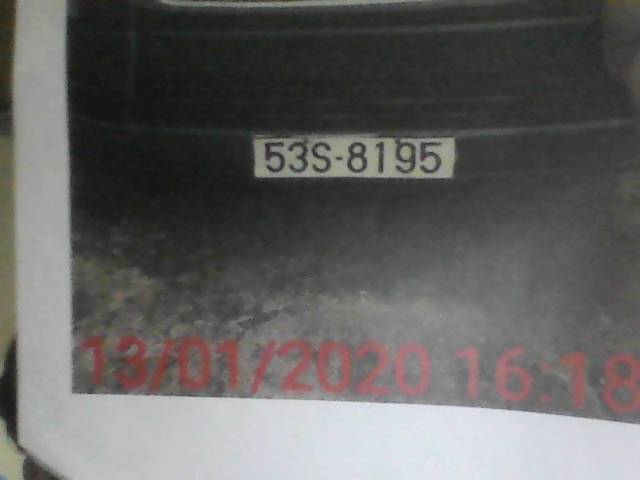
back_end/uploads/1747044213636-entry-1747044213633.jpg
