hutuswatermelon/NT131.P22/back_end/uploads/1747046811432-entry-1747046811428.jpg

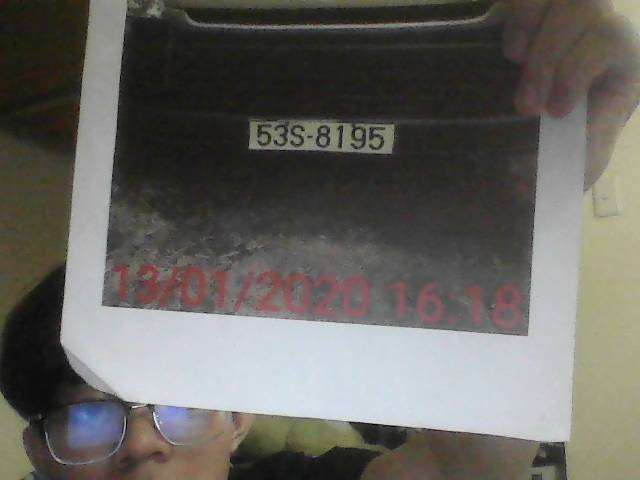
back_end/uploads/1747046811432-entry-1747046811428.jpg
