hutuswatermelon/NT131.P22/back_end/uploads/1747048586695-entry-1747048586691.jpg

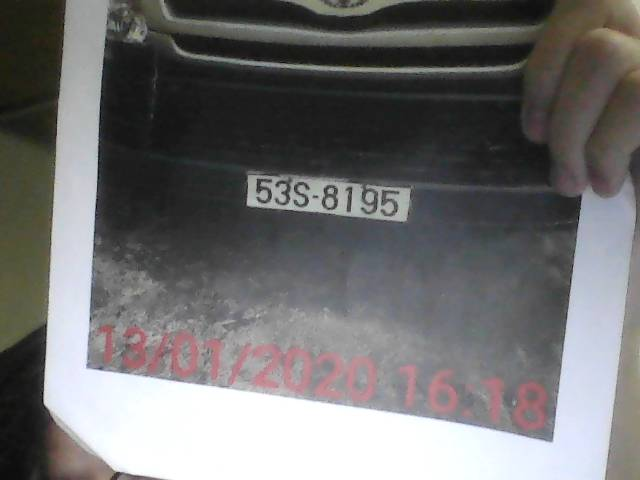
back_end/uploads/1747048586695-entry-1747048586691.jpg
