hutuswatermelon/NT131.P22/back_end/uploads/1747049174839-entry-1747049174822.jpg

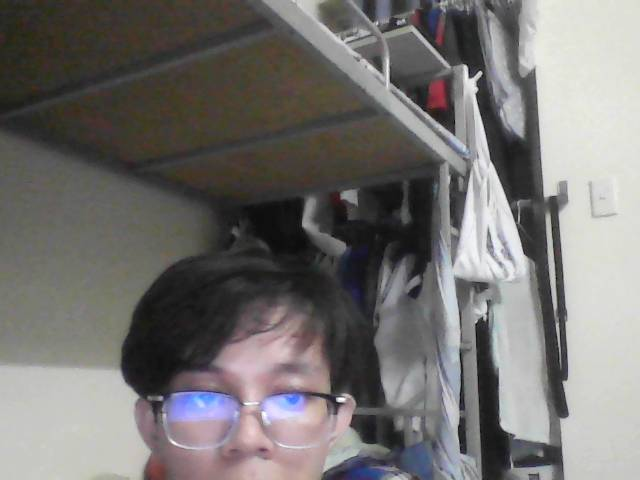
back_end/uploads/1747049174839-entry-1747049174822.jpg
