hutuswatermelon/NT131.P22/back_end/uploads/1747055420367-entry-1747055420354.jpg

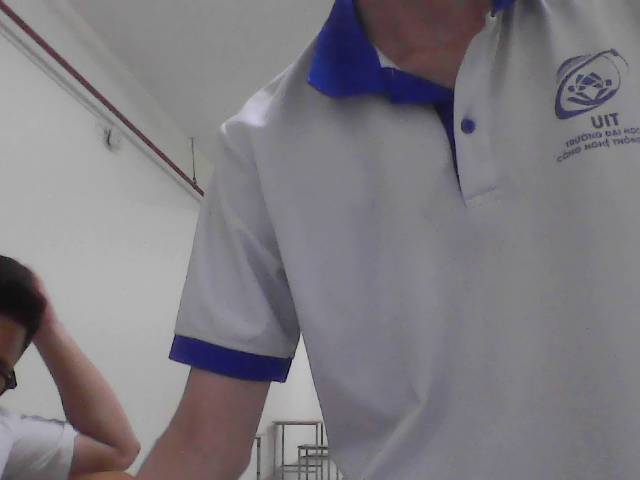
back_end/uploads/1747055420367-entry-1747055420354.jpg
