hutuswatermelon/NT131.P22/back_end/uploads/1747056215381-entry-1747056215357.jpg

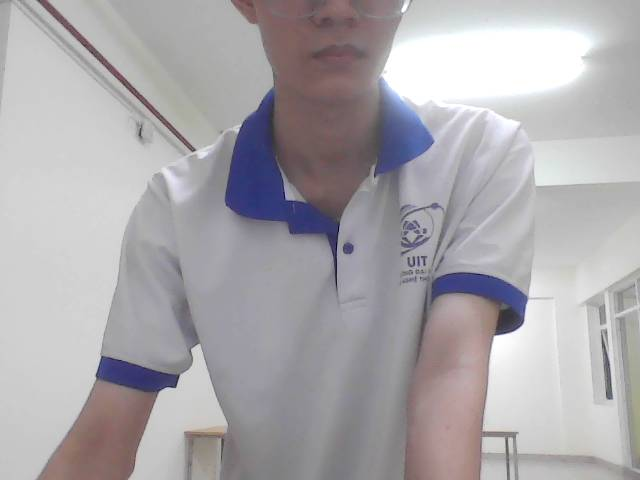
back_end/uploads/1747056215381-entry-1747056215357.jpg
