hutuswatermelon/NT131.P22/back_end/uploads/1747057412438-entry-1747057412425.jpg

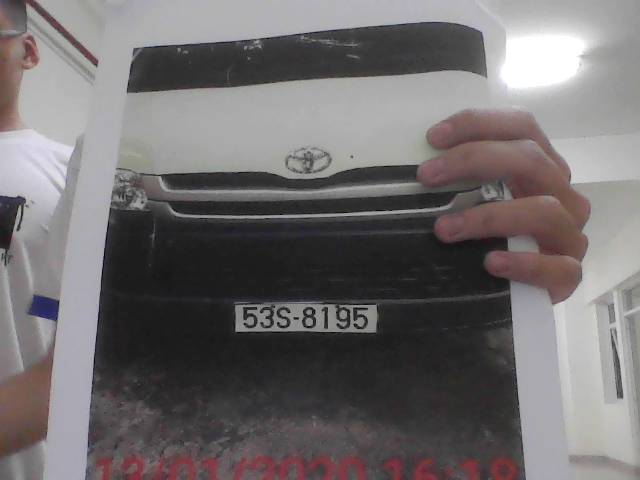
back_end/uploads/1747057412438-entry-1747057412425.jpg
