hutuswatermelon/NT131.P22/back_end/uploads/1747057524411-exit-1747057524407.jpg

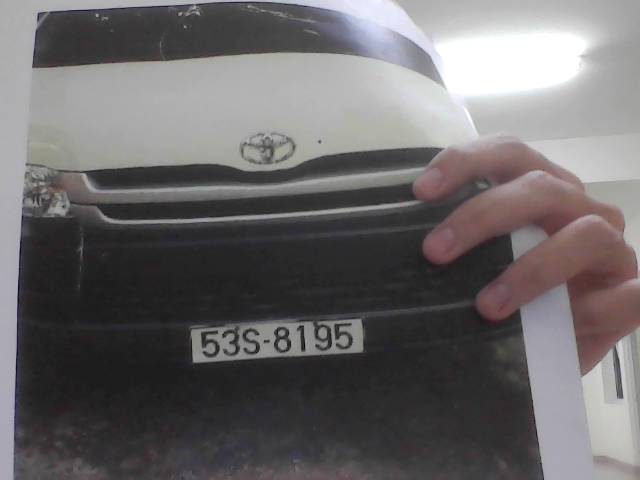
back_end/uploads/1747057524411-exit-1747057524407.jpg
