hutuswatermelon/NT131.P22/back_end/uploads/1747057537004-exit-1747057537000.jpg

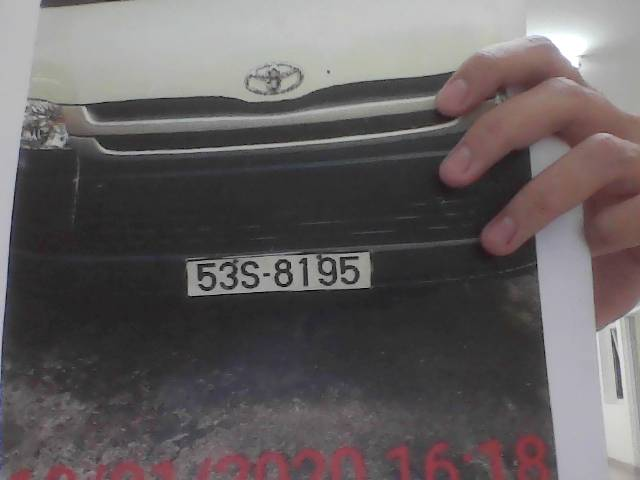
back_end/uploads/1747057537004-exit-1747057537000.jpg
