hutuswatermelon/NT131.P22/back_end/uploads/1747057549745-exit-1747057549740.jpg

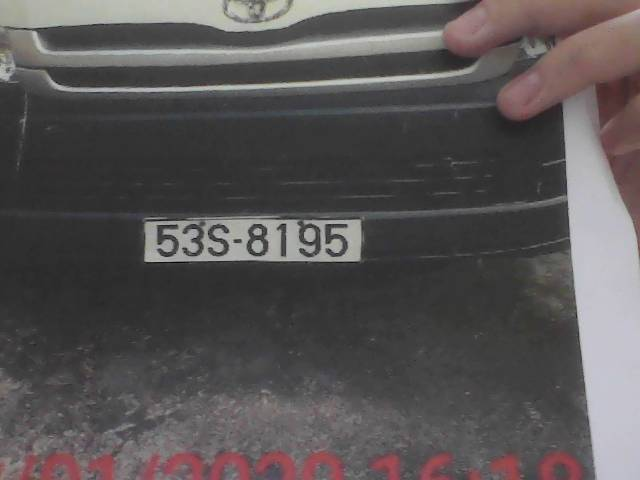
back_end/uploads/1747057549745-exit-1747057549740.jpg
